maxmar391/robotic_biped/CAD/original/servo_horn_spacer.stl

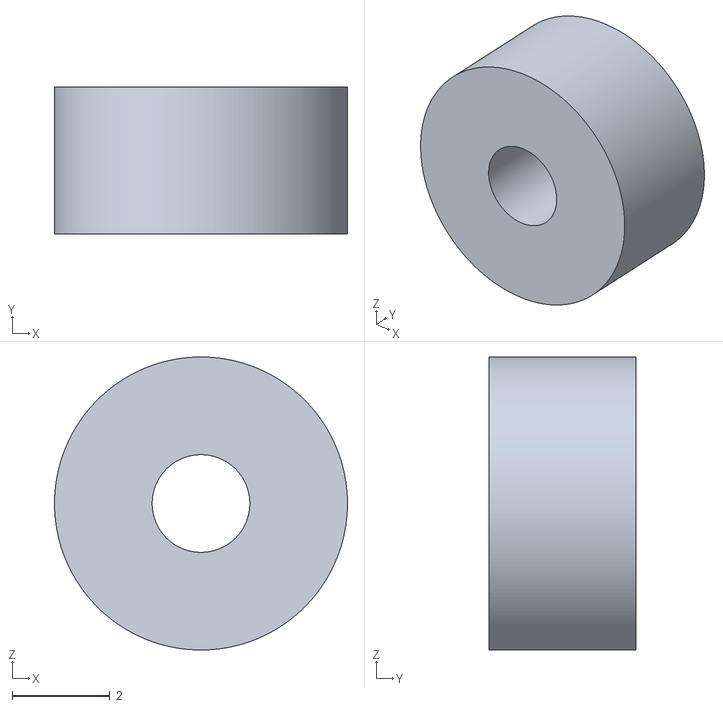
[picture p66: CAD file, 2020-11-25]
CAD/original/servo_horn_spacer.stl
6.00 x 3.00 x 6.00
