maxmar391/robotic_biped/CAD/original/knee_servo_holder_mirror.stl

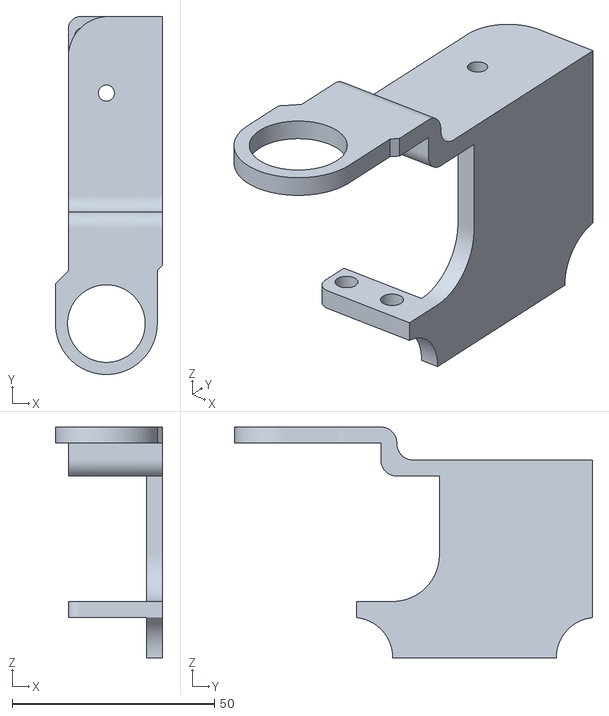
[picture p67: CAD file, 2020-11-25]
CAD/original/knee_servo_holder_mirror.stl
26.5 x 88.6 x 57.2
